internettrashh/ukmarsbot-mini/half-size-mech-prototypes/output_files/prototype1.stl

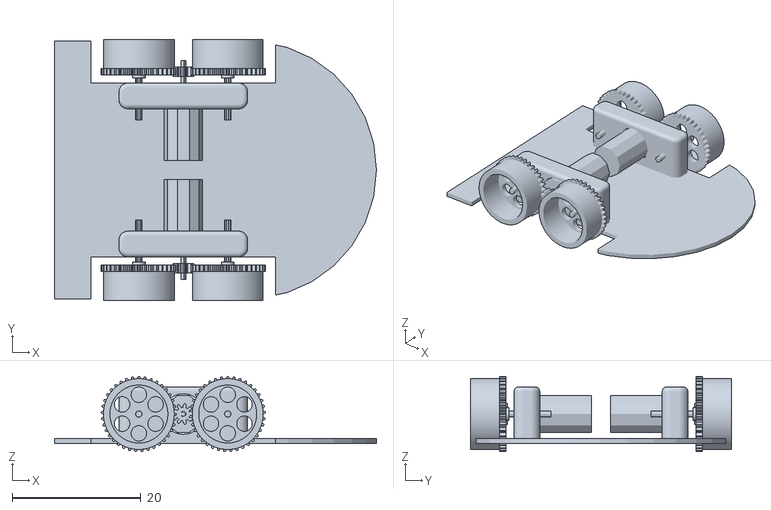
[picture p21: CAD file, 2021-08-22]
half-size-mech-prototypes/output_files/prototype1.stl
50.0 x 40.5 x 11.7
