internettrashh/ukmarsbot-mini/half-size-mech-prototypes/output_files/gears_prototype1.stl

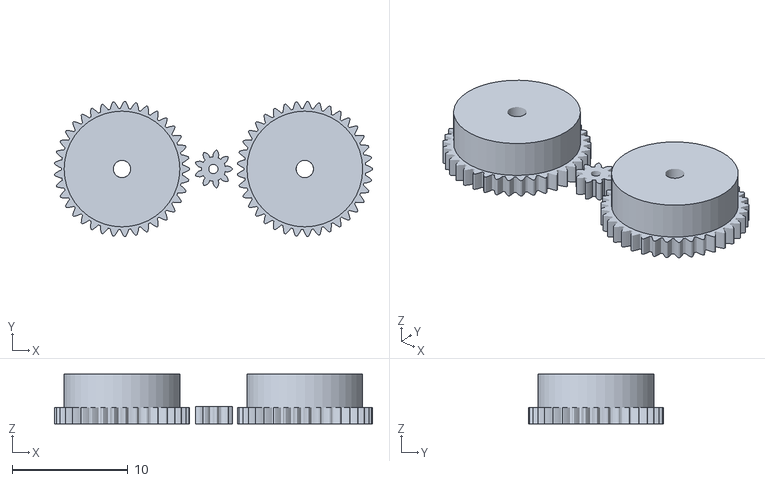
[picture p22: CAD file, 2021-08-22]
half-size-mech-prototypes/output_files/gears_prototype1.stl
27.5 x 11.7 x 4.30
